paulh002/VFO-ESP32-Si5351/Kicad/output.png

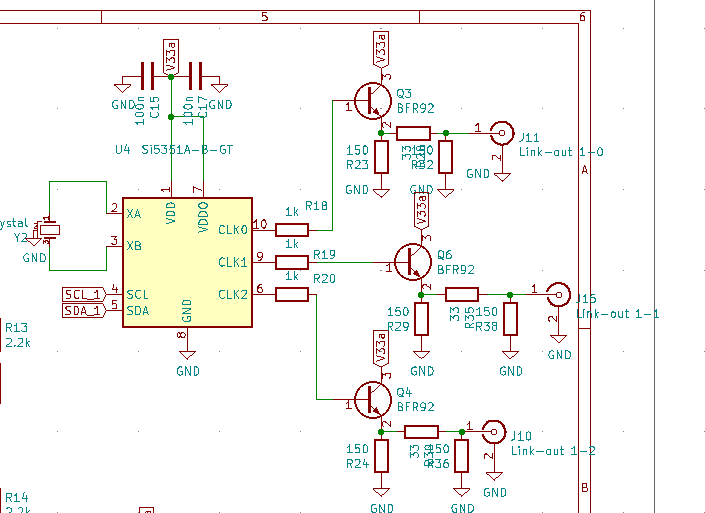
Kicad/output.png
