paulh002/VFO-ESP32-Si5351/VFO_PCB3.jpg

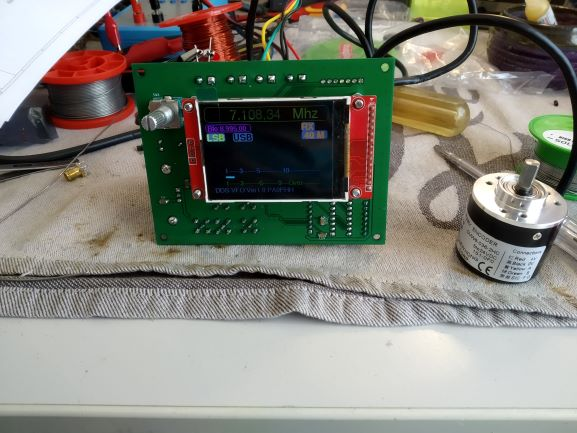
VFO_PCB3.jpg
